LaplandUAS/FrostDisc/src/toHex.h

/*
 * toHex.h
 *
 * Created: 6.10.2023 14.57.00
 * Author : Jessé Forest
 */

#ifndef TOHEX_H_
#define TOHEX_H_

#define ZERO_PAD 1

#include <stdint.h>

char* itohexa (char dest[5], uint16_t x);
#endif /* TOHEX_H_ */
